numberformat/noami3/stl/lcd-support-B.stl

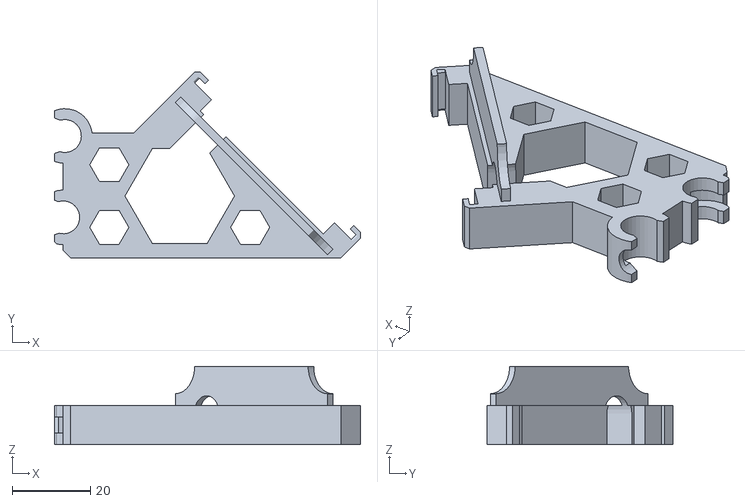
[picture p19: CAD file, 2020-07-04]
stl/lcd-support-B.stl
78.2 x 47.5 x 20.0
