numberformat/noami3/STEP/y-motor-holder.stp

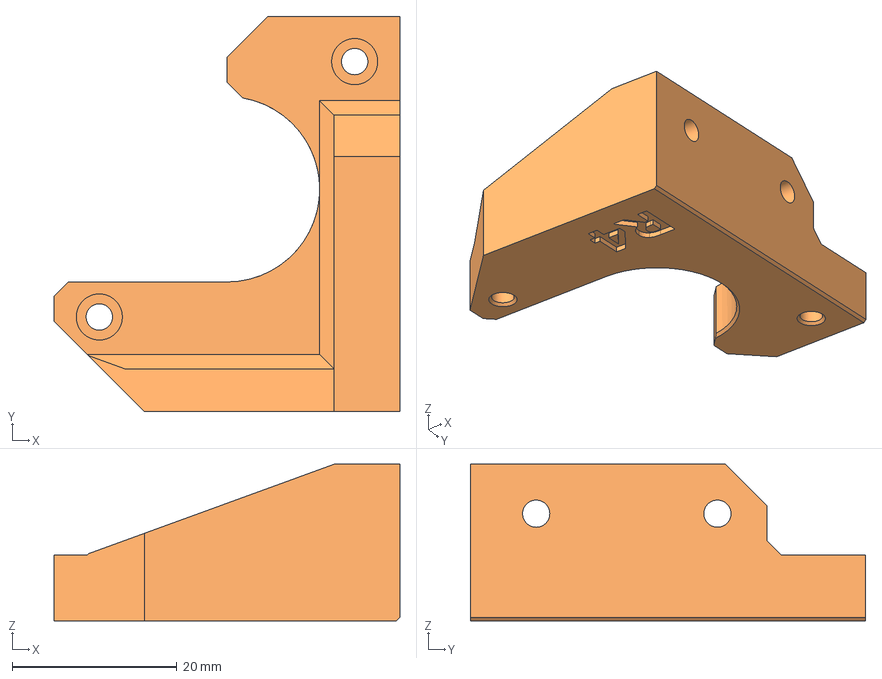
[picture p20: CAD file, 2020-06-21]
STEP/y-motor-holder.stp
42.0 x 48.0 x 19.0 mm
