numberformat/noami3/STEP/fs-lever.stp

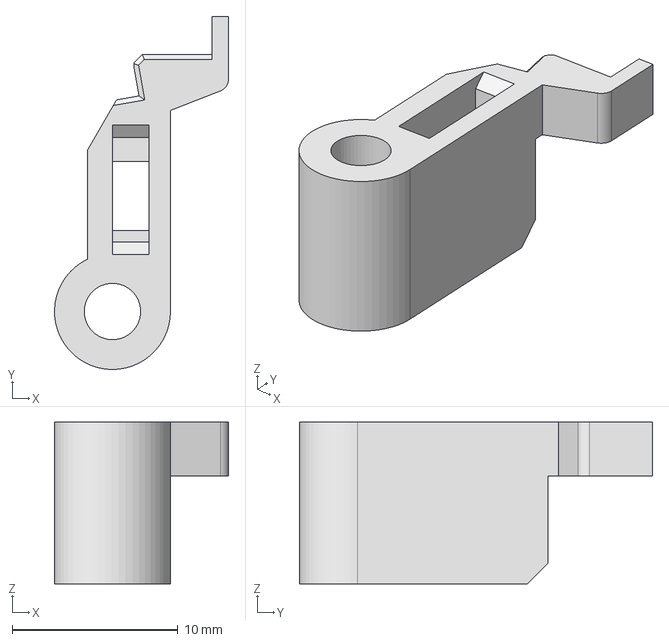
[picture p22: CAD file, 2020-06-21]
STEP/fs-lever.stp
10.5 x 21.3 x 9.75 mm
