numberformat/noami3/stl/mks-gen1_4-base.stl

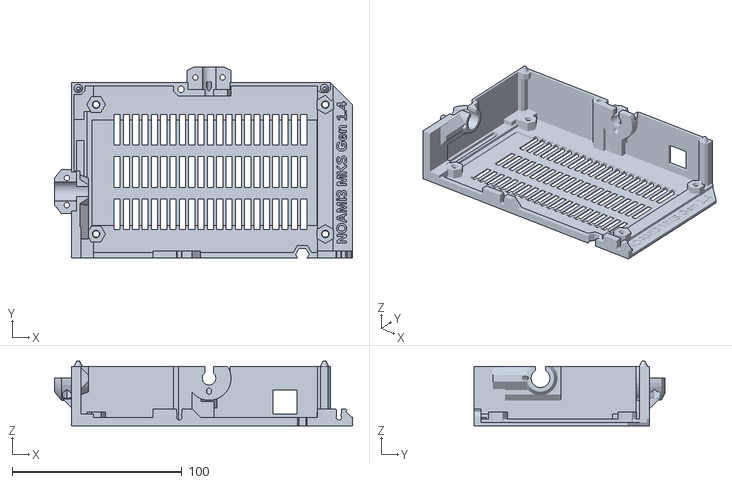
[picture p23: CAD file, 2020-06-30]
stl/mks-gen1_4-base.stl
175.5 x 112.2 x 38.0
