numberformat/noami3/STEP/ir-sensor-holder-mmu2s.stp

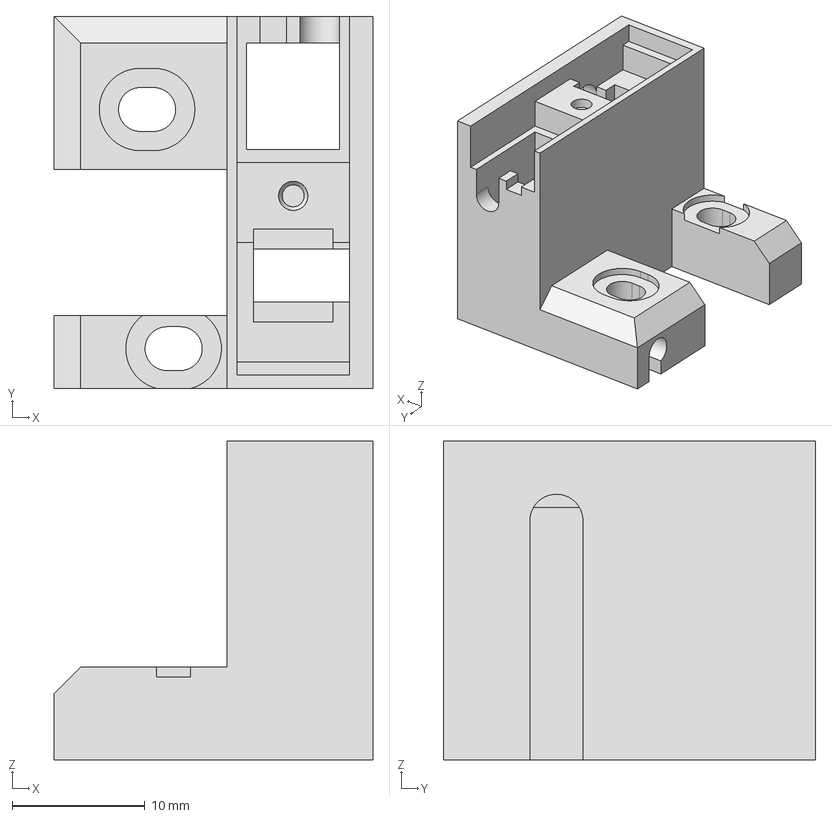
[picture p24: CAD file, 2020-06-21]
STEP/ir-sensor-holder-mmu2s.stp
24.0 x 28.0 x 24.0 mm
