numberformat/noami3/stl/mks-gen1_4-cover-doors-mk3-frame.stl

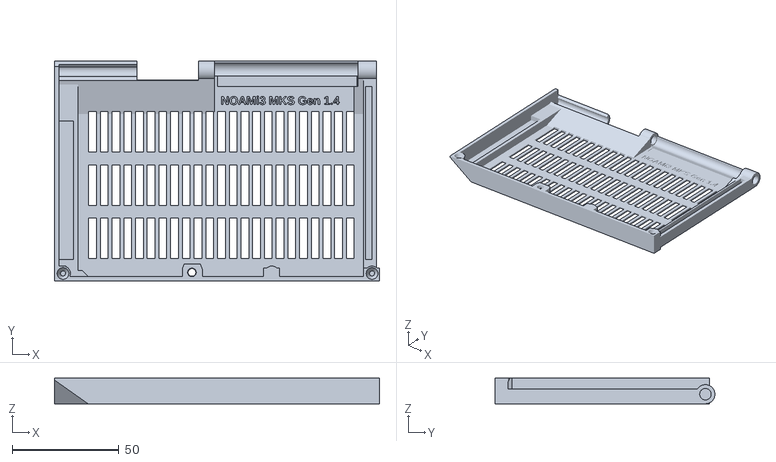
[picture p25: CAD file, 2020-06-30]
stl/mks-gen1_4-cover-doors-mk3-frame.stl
152.5 x 103.2 x 12.0
