numberformat/noami3/STEP/fan-shroud.stp

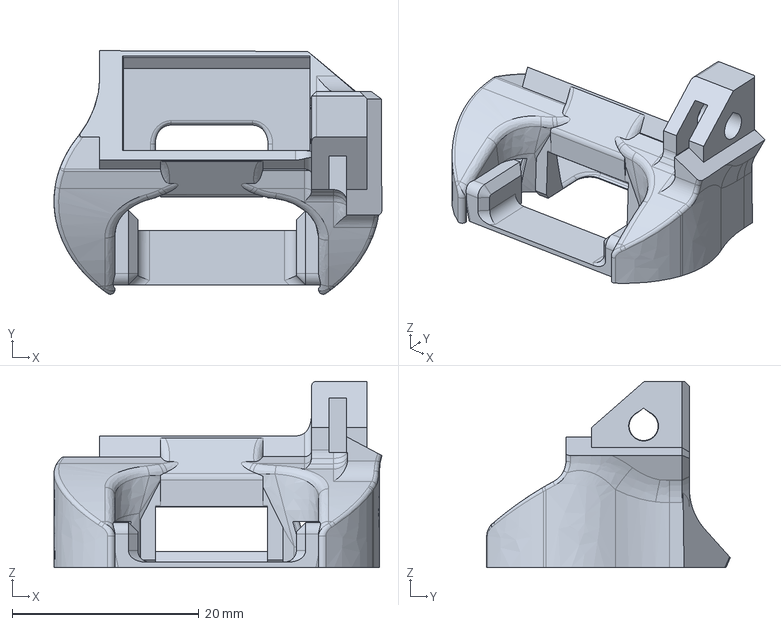
[picture p26: CAD file, 2020-06-21]
STEP/fan-shroud.stp
35.2 x 26.1 x 20.0 mm
