numberformat/noami3/stl/mks-gen1_4-cover-doors.stl

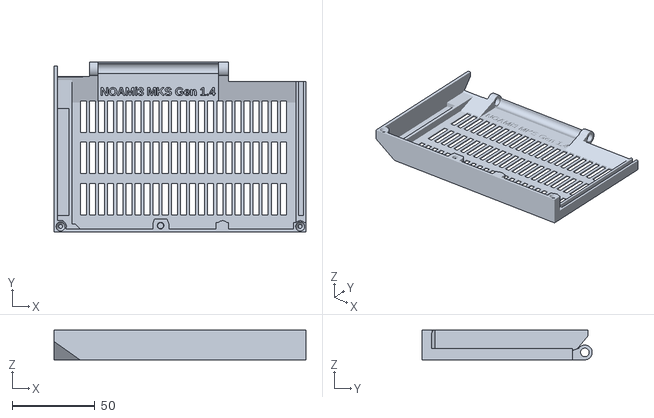
[picture p27: CAD file, 2020-06-30]
stl/mks-gen1_4-cover-doors.stl
152.5 x 103.2 x 18.0
