numberformat/noami3/stl/cable-holder.stl

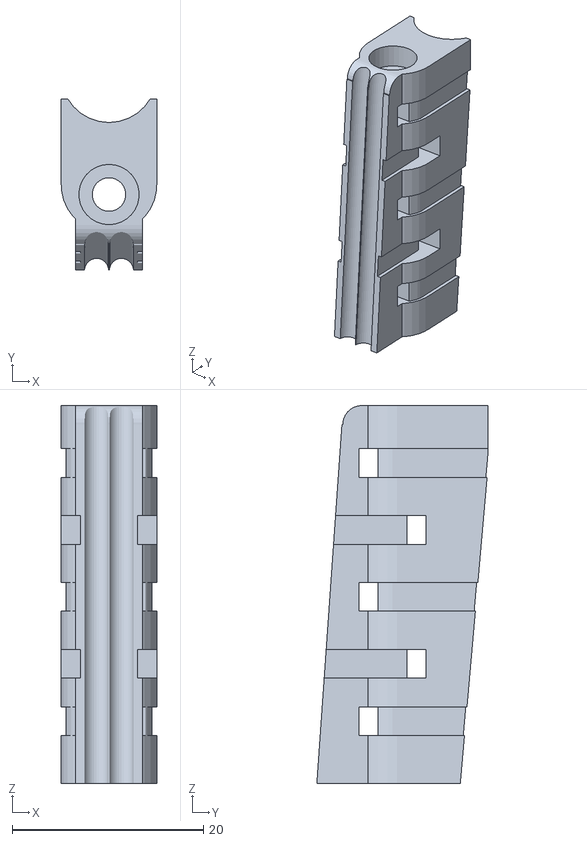
[picture p29: CAD file, 2020-06-25]
stl/cable-holder.stl
10.0 x 17.9 x 39.5
