numberformat/noami3/STEP/fs-cover-mmu2s.stp

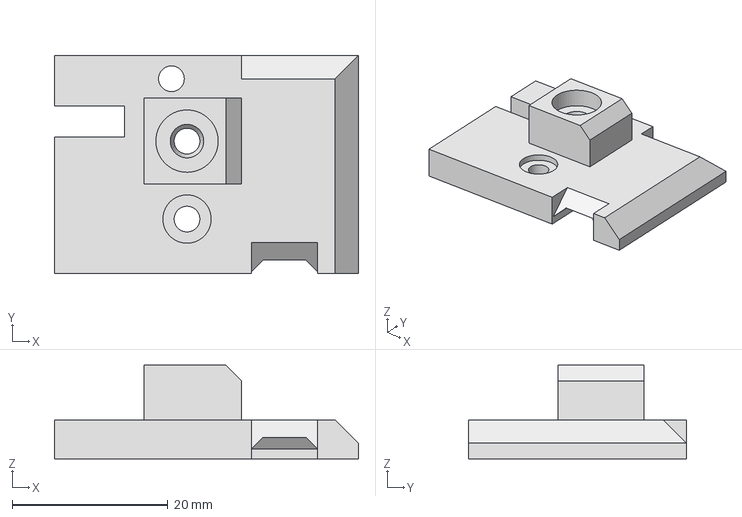
[picture p30: CAD file, 2020-06-21]
STEP/fs-cover-mmu2s.stp
39.0 x 28.0 x 12.0 mm
