numberformat/noami3/stl/x-carriage-with-tab.stl

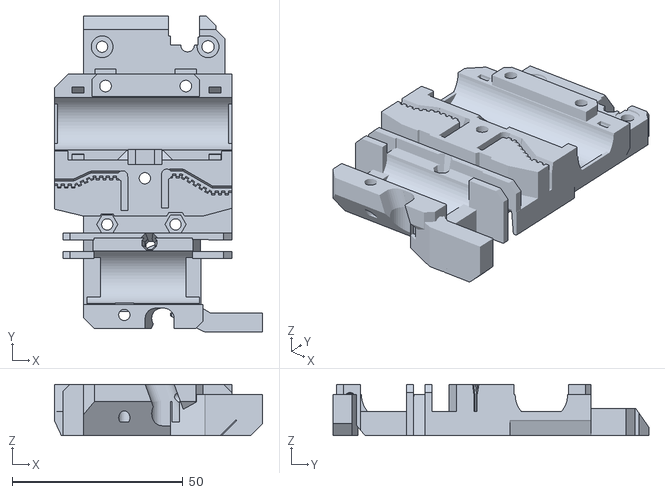
[picture p31: CAD file, 2020-06-25]
stl/x-carriage-with-tab.stl
61.0 x 92.5 x 15.0
