numberformat/noami3/STEP/extruder-motor-plate.stp

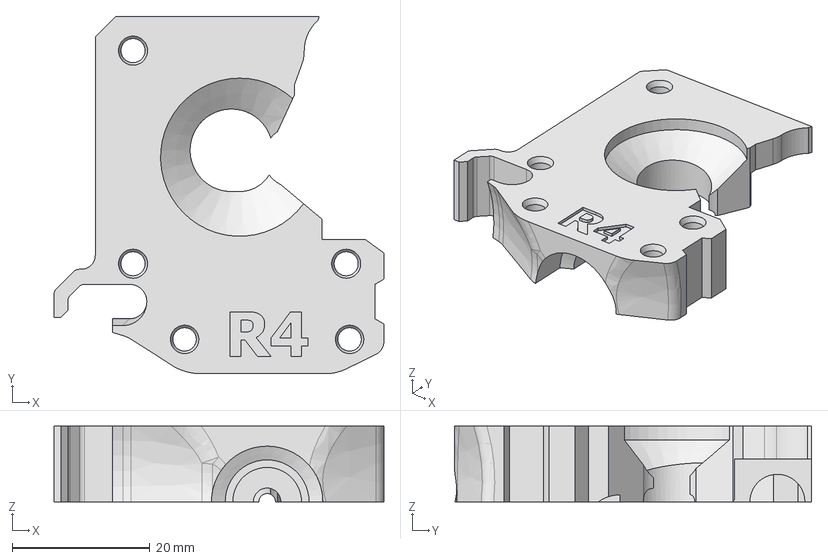
[picture p32: CAD file, 2020-06-21]
STEP/extruder-motor-plate.stp
48.0 x 52.0 x 11.0 mm
