numberformat/noami3/stl/mks-gen1_4-Hinges.stl

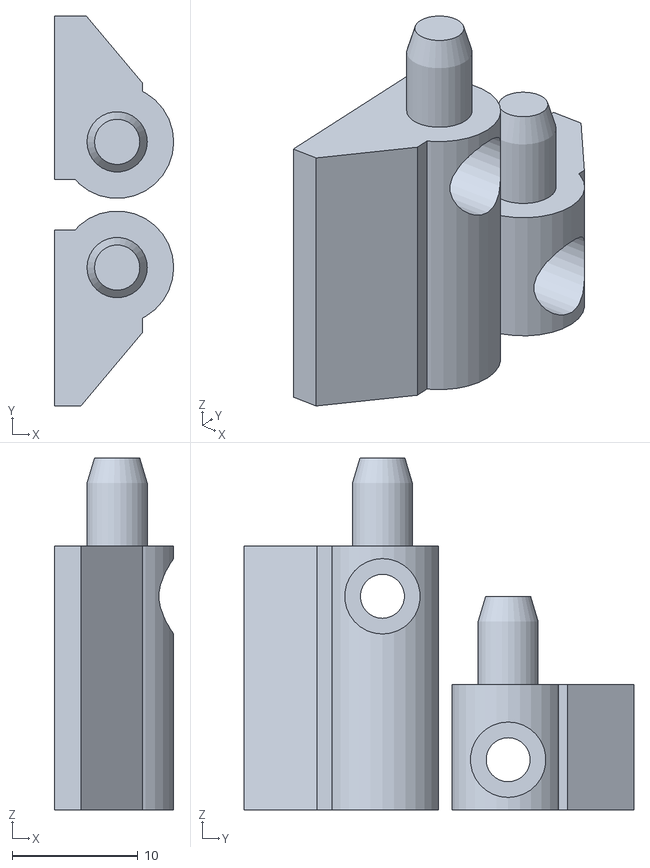
[picture p33: CAD file, 2020-06-25]
stl/mks-gen1_4-Hinges.stl
9.50 x 31.0 x 28.0
