numberformat/noami3/STEP/psu-cover-DELTA.step

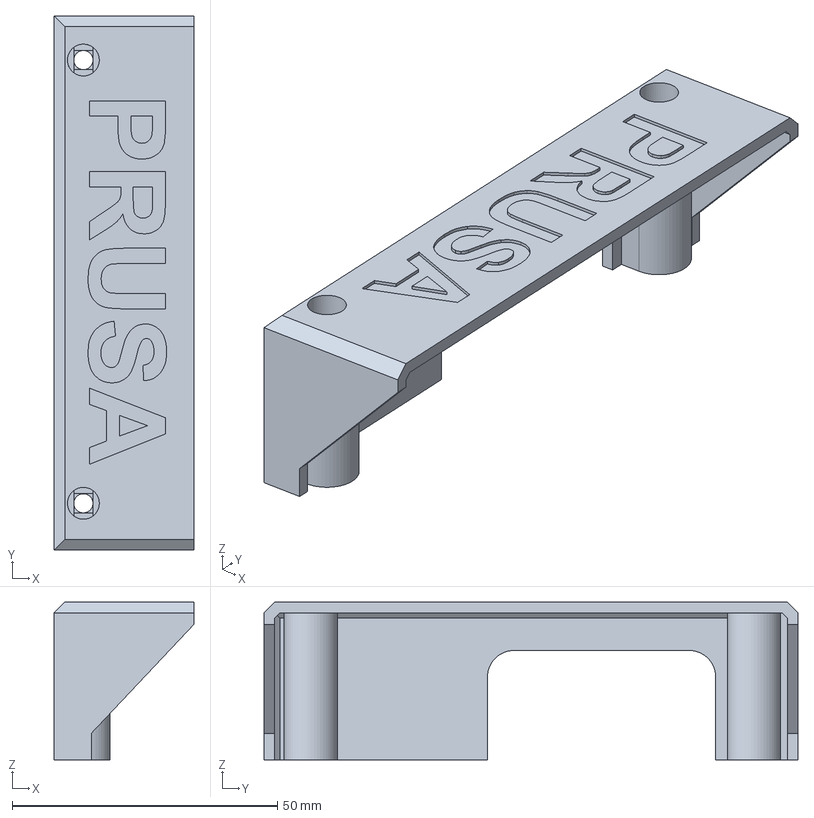
[picture p34: CAD file, 2020-06-21]
STEP/psu-cover-DELTA.step
26.3 x 100.6 x 29.7 mm
