numberformat/noami3/STEP/extruder-body.stp

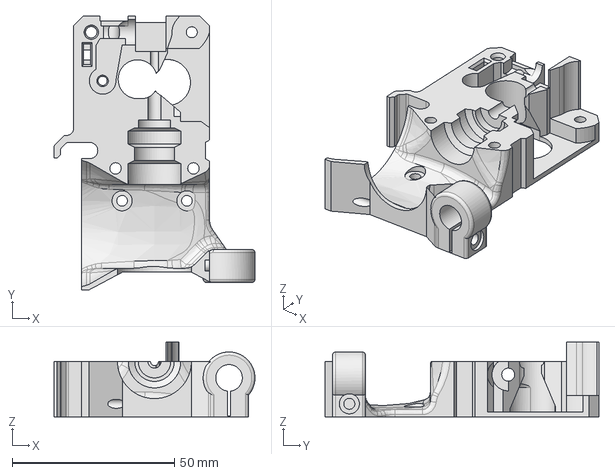
[picture p35: CAD file, 2020-06-21]
STEP/extruder-body.stp
62.0 x 84.5 x 23.0 mm
