numberformat/noami3/stl/extruder-idler.stl

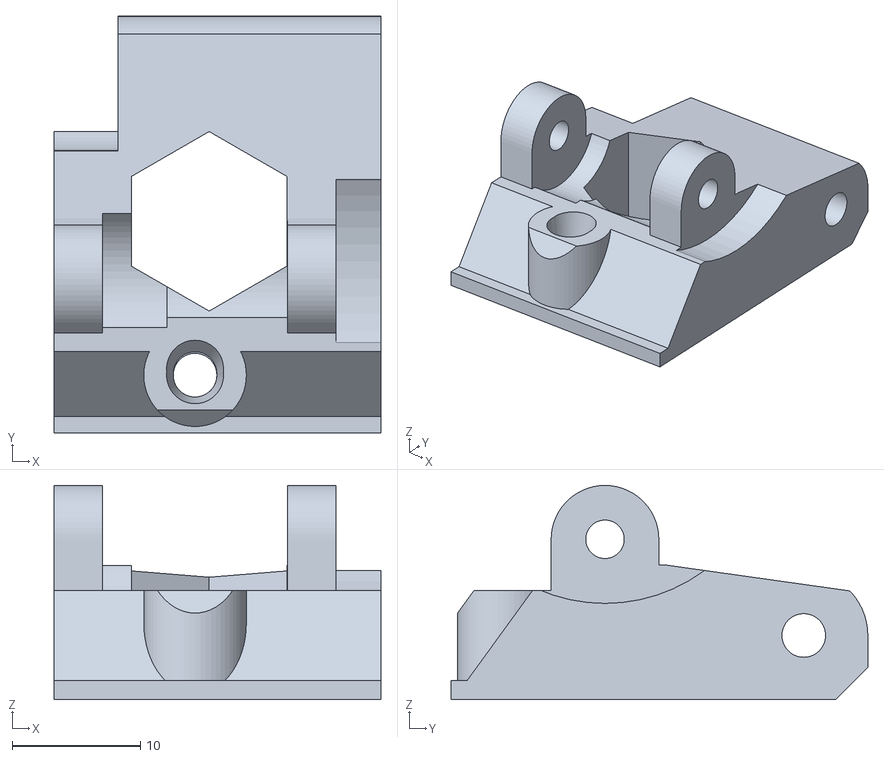
[picture p36: CAD file, 2020-06-21]
stl/extruder-idler.stl
25.5 x 32.5 x 16.7
