numberformat/noami3/STEP/adapter-printer-mmu2s.stp

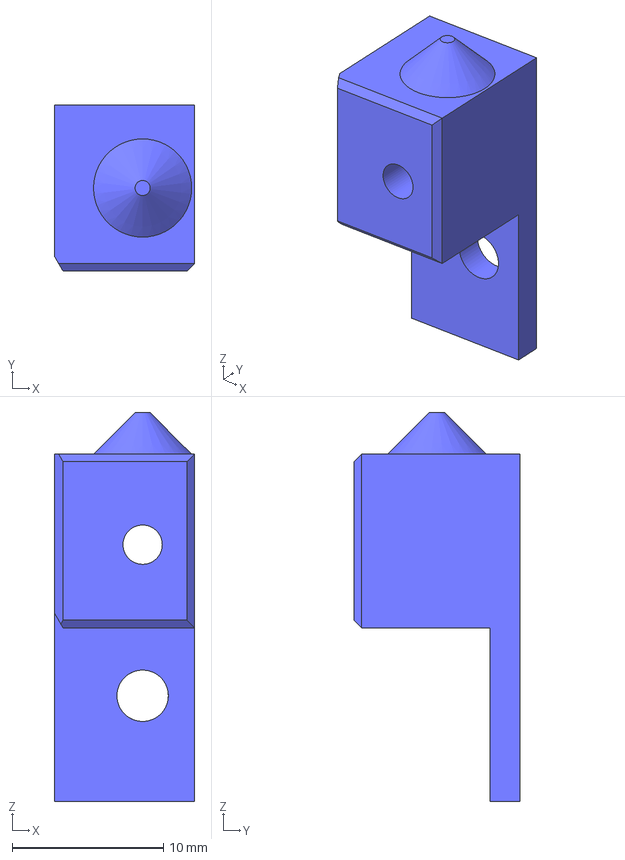
[picture p37: CAD file, 2020-06-21]
STEP/adapter-printer-mmu2s.stp
9.30 x 11.0 x 25.8 mm
