numberformat/noami3/stl/LCD-knob.stl

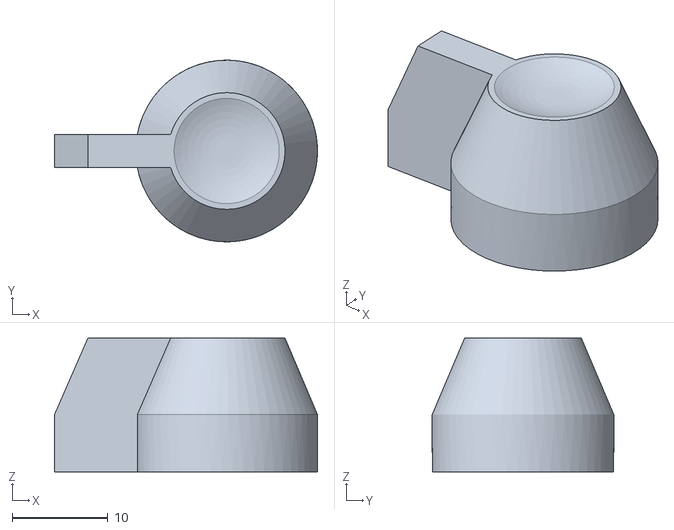
[picture p38: CAD file, 2020-06-21]
stl/LCD-knob.stl
27.5 x 19.0 x 14.0
