numberformat/noami3/STEP/extruder-cover.stp

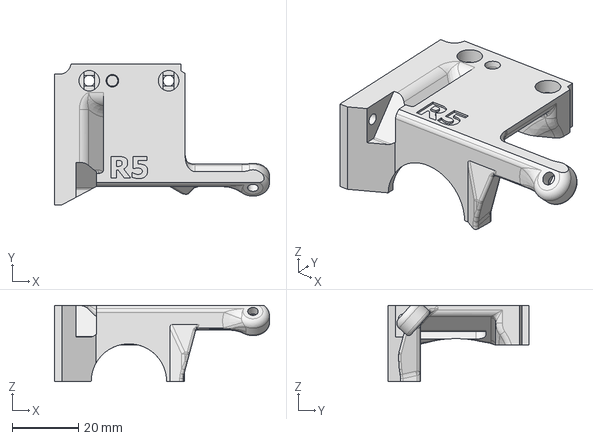
[picture p39: CAD file, 2020-06-21]
STEP/extruder-cover.stp
65.0 x 42.5 x 23.0 mm
