numberformat/noami3/stl/y-motor.stl

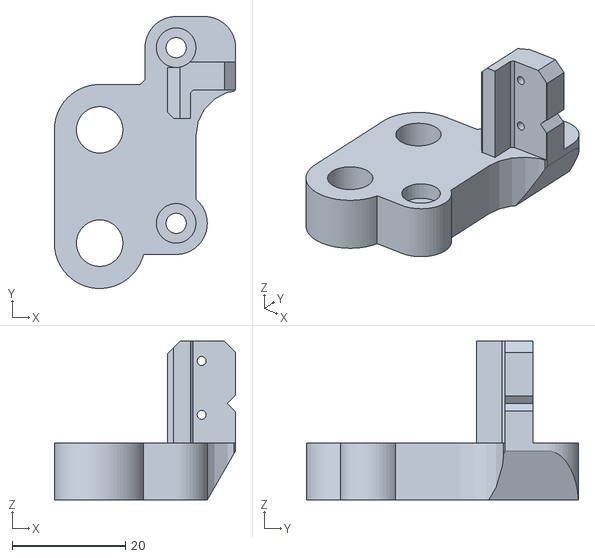
[picture p40: CAD file, 2020-06-21]
stl/y-motor.stl
32.0 x 48.0 x 28.0
