numberformat/noami3/STEP/y-belt-holder.stp

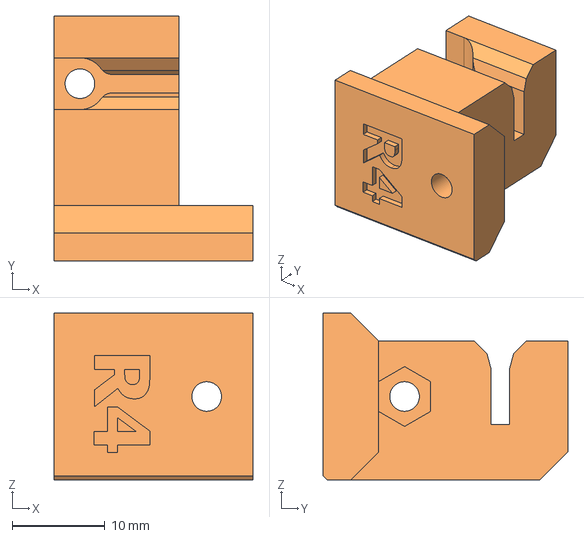
[picture p41: CAD file, 2020-06-21]
STEP/y-belt-holder.stp
21.5 x 26.4 x 18.0 mm
