numberformat/noami3/stl/x-carriage-needs update.stl

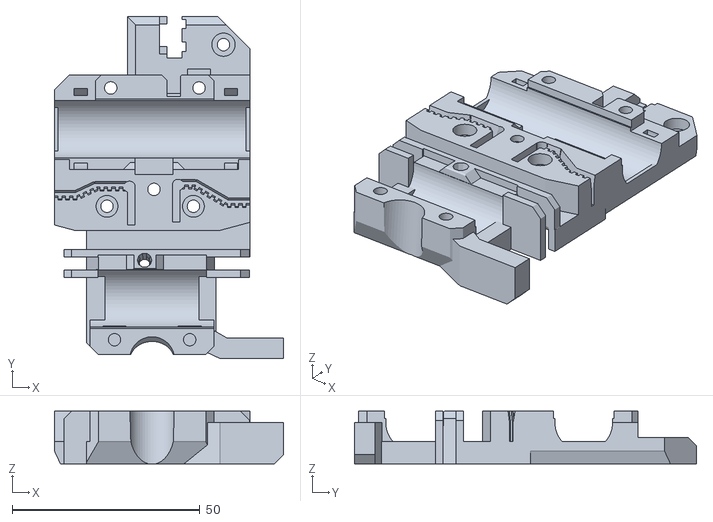
[picture p42: CAD file, 2020-06-21]
stl/x-carriage-needs update.stl
61.0 x 91.0 x 14.0
