numberformat/noami3/stl/x-end-motor.stl

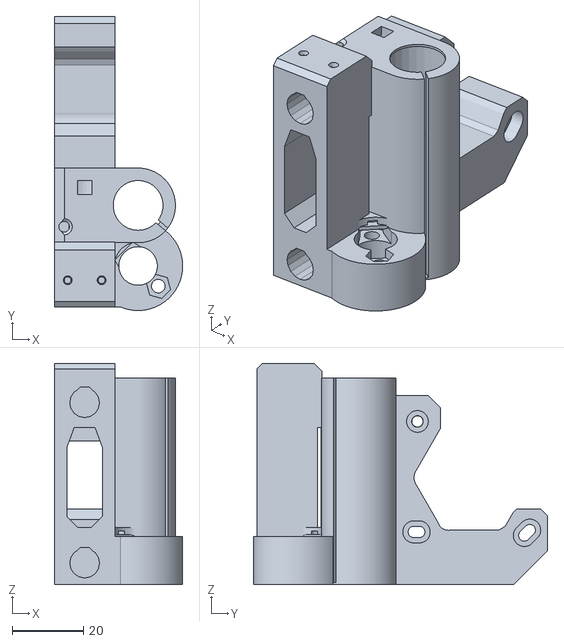
[picture p43: CAD file, 2020-06-21]
stl/x-end-motor.stl
36.0 x 82.5 x 62.0
