numberformat/noami3/stl/print-fan-support.stl

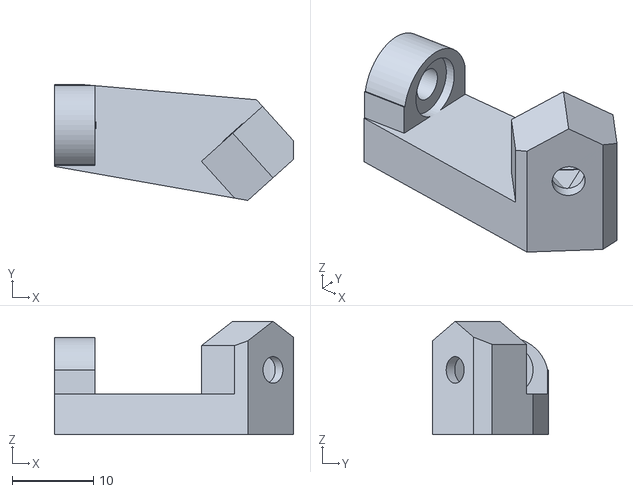
[picture p44: CAD file, 2020-06-21]
stl/print-fan-support.stl
29.5 x 14.3 x 14.0
