numberformat/noami3/stl/x-carriage-back.stl

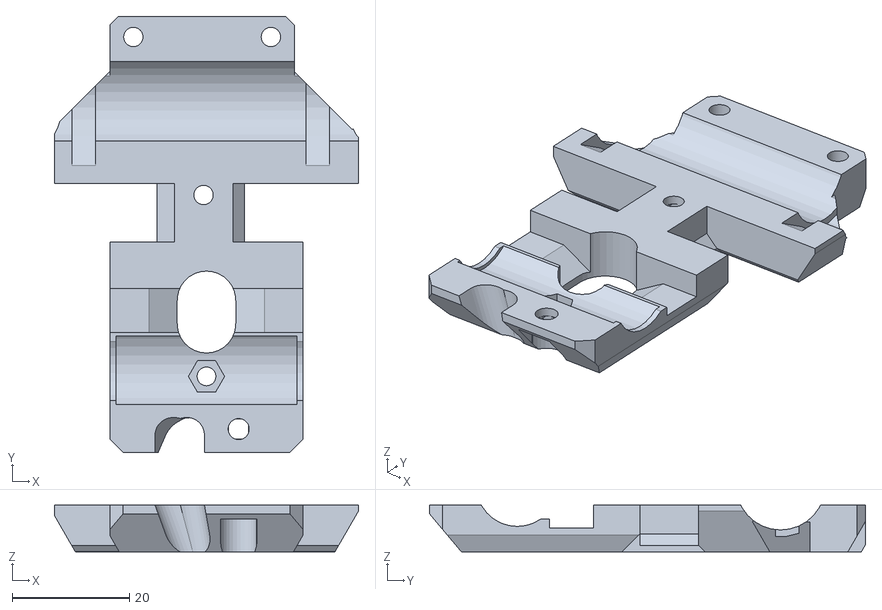
[picture p45: CAD file, 2020-06-21]
stl/x-carriage-back.stl
52.0 x 74.5 x 8.00
