numberformat/noami3/stl/PSU-Cover-NOAMi3.stl

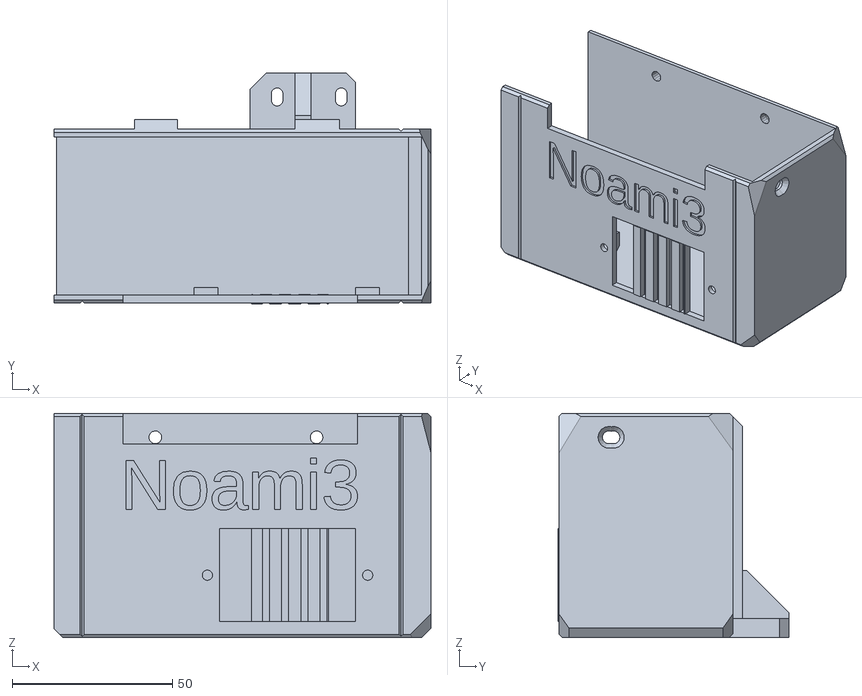
[picture p46: CAD file, 2020-06-21]
stl/PSU-Cover-NOAMi3.stl
117.6 x 72.1 x 70.0
