numberformat/noami3/stl/LCD-cable-clip-imp.stl

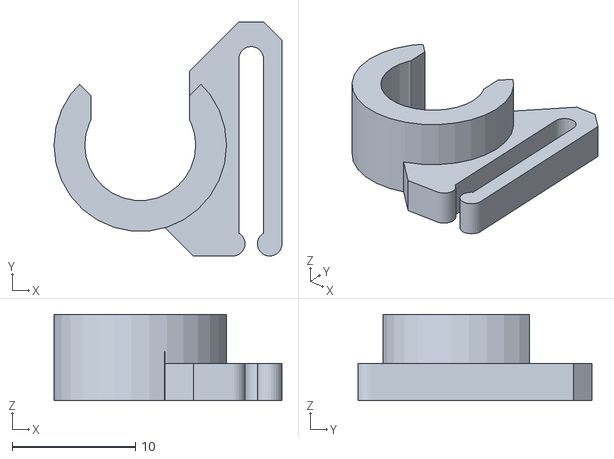
[picture p47: CAD file, 2020-06-21]
stl/LCD-cable-clip-imp.stl
18.5 x 19.0 x 7.00
