numberformat/noami3/stl/fs-cover.stl

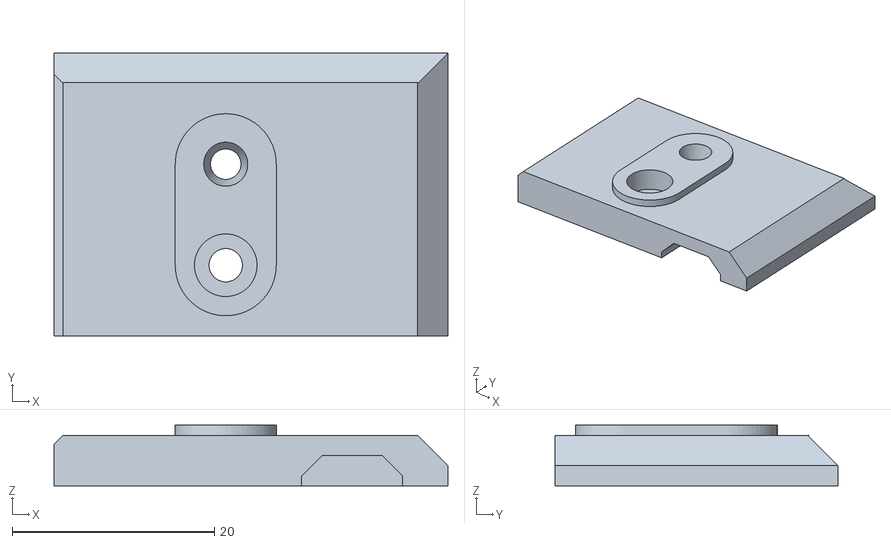
[picture p48: CAD file, 2020-06-21]
stl/fs-cover.stl
39.0 x 28.0 x 6.00
