numberformat/noami3/stl/LCD-cover-NOAMI3.stl

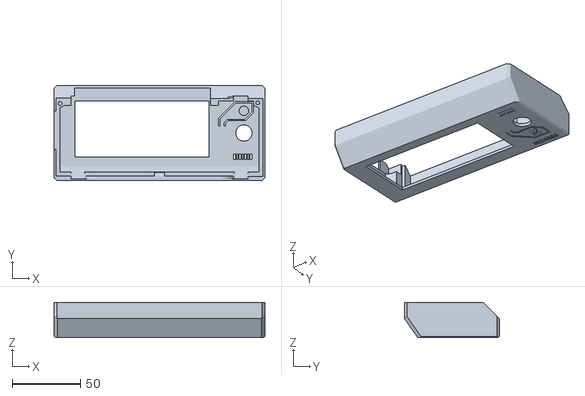
[picture p49: CAD file, 2020-06-21]
stl/LCD-cover-NOAMI3.stl
155.0 x 70.0 x 26.0
