numberformat/noami3/stl/y-idler.stl

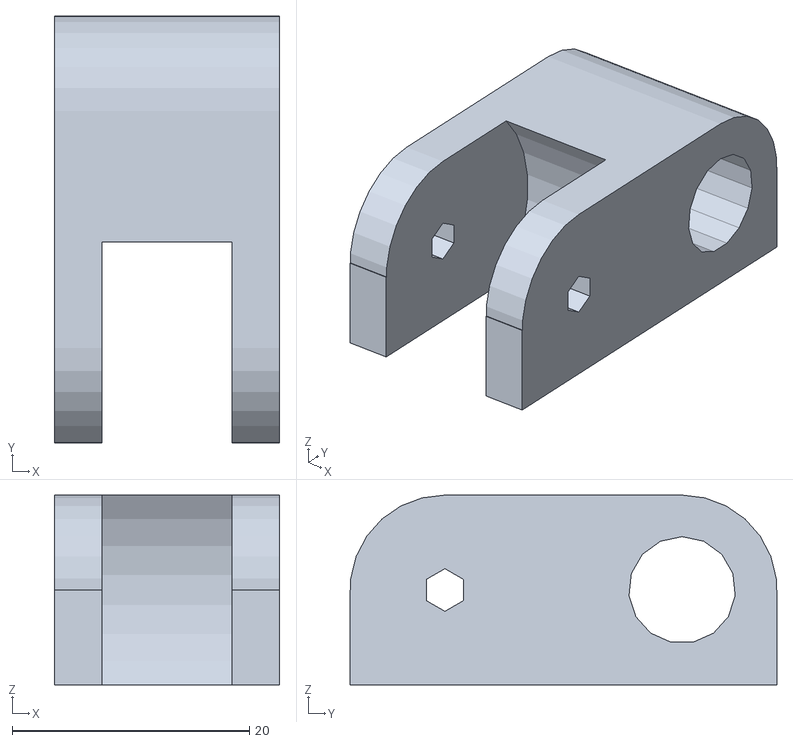
[picture p50: CAD file, 2020-02-16]
stl/y-idler.stl
19.0 x 36.0 x 16.0
