numberformat/noami3/stl/LCD-cable-clip.stl

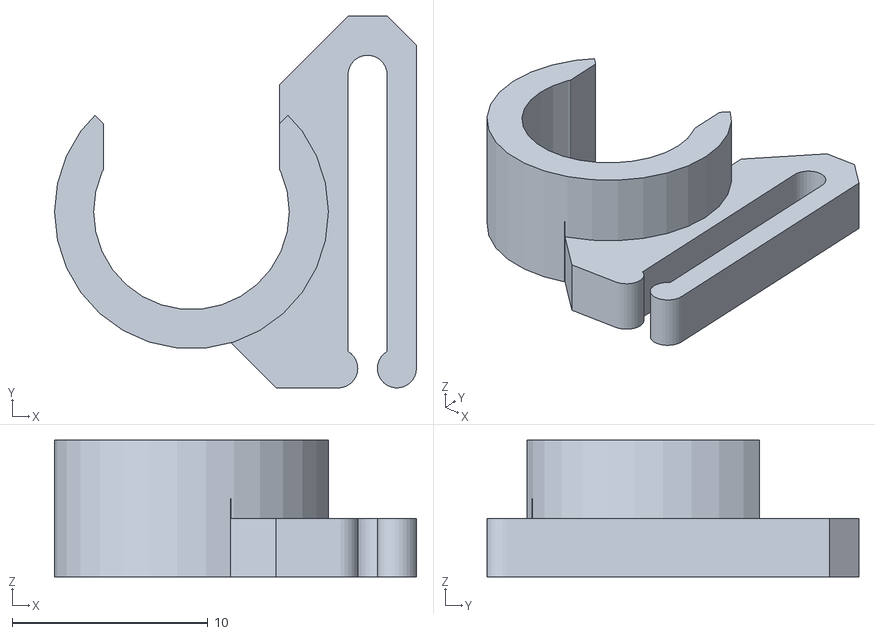
[picture p51: CAD file, 2020-02-16]
stl/LCD-cable-clip.stl
18.5 x 19.0 x 7.00
