numberformat/noami3/stl/y-corners-imperial.stl

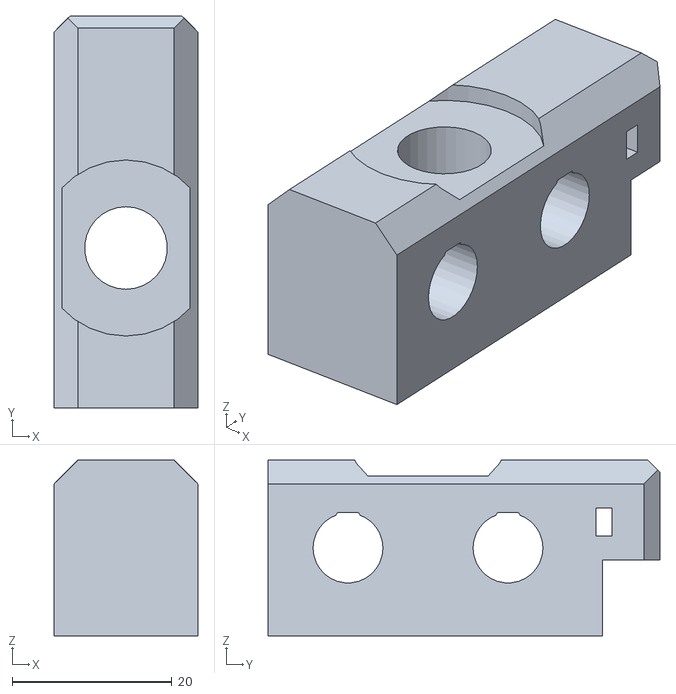
[picture p52: CAD file, 2020-02-16]
stl/y-corners-imperial.stl
18.0 x 49.0 x 22.0
