numberformat/noami3/stl/ramps-enclosure.STL

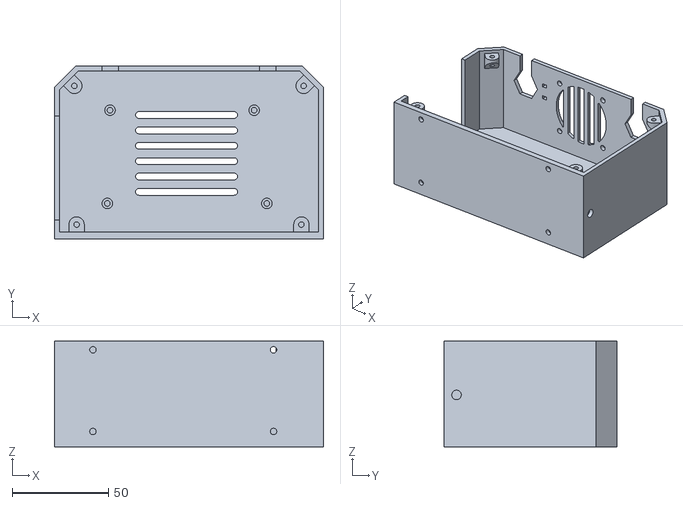
[picture p53: CAD file, 2020-02-16]
stl/ramps-enclosure.STL
140.0 x 90.0 x 55.0
