numberformat/noami3/stl/ramps-enclosure-cover.STL

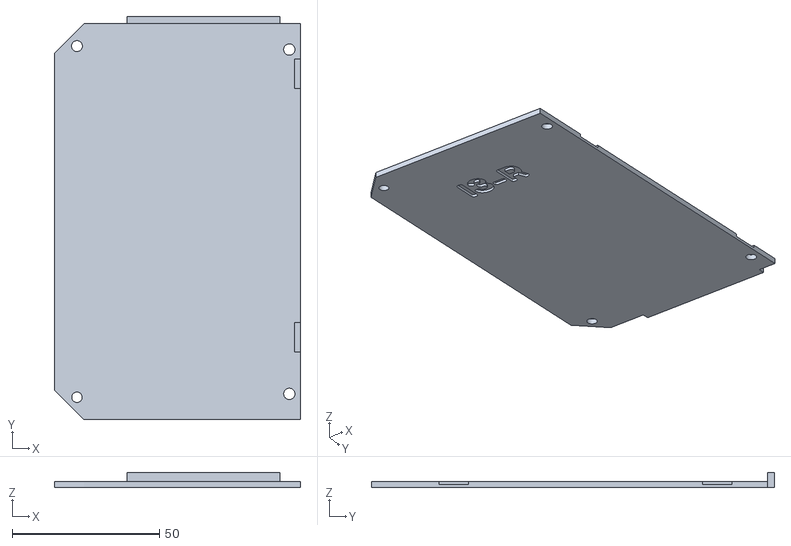
[picture p54: CAD file, 2020-02-16]
stl/ramps-enclosure-cover.STL
83.6 x 137.1 x 5.00
