numberformat/noami3/stl/PSU-Y-part-imperial.stl

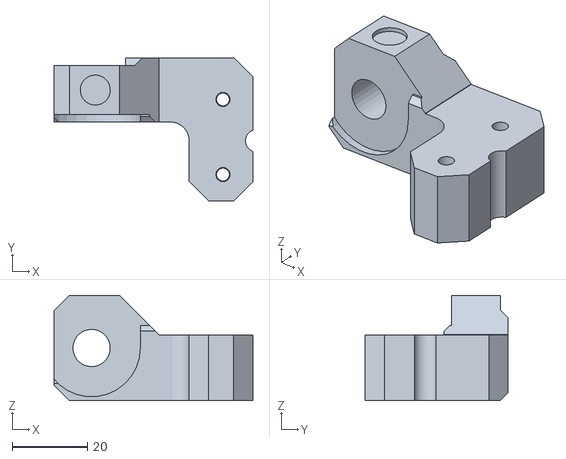
[picture p55: CAD file, 2020-02-16]
stl/PSU-Y-part-imperial.stl
53.0 x 38.0 x 28.0
