numberformat/noami3/stl/z-axis-top.stl

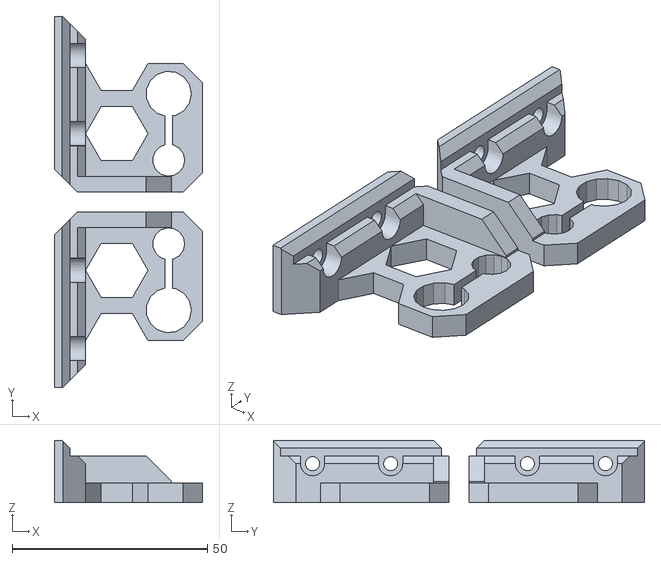
[picture p56: CAD file, 2020-02-16]
stl/z-axis-top.stl
38.0 x 95.0 x 16.0
