numberformat/noami3/stl/z-axis-bottom.stl

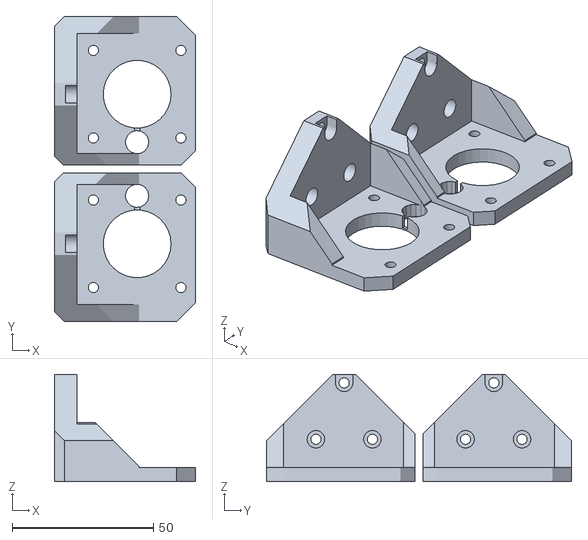
[picture p58: CAD file, 2020-02-16]
stl/z-axis-bottom.stl
50.0 x 108.0 x 38.0
