numberformat/noami3/scad/OpenSCAD_3dprinter/right-side/cube.scad

difference()
{    
    cube([7,7,3],center=true);
    cylinder(d=3,h=8,$fn=25,center=true);    
}   
