numberformat/noami3/scad/OpenSCAD_3dprinter/right-side/nut-trap.scad

difference() {
    cube([15,15,5], center=true);
    rotate([0, 0, -135]) rotate([0, 0, 0])cylinder(h = 6, r = 3.6, $fn=6);    
}
